meerstern/Nano_USB_Scroller/firm/mouse.c

#include <stdint.h>
#include <string.h>
#include "ch554.h"
#include "ch554_usb.h"
#include "mouse.h"

#define UsbSetupBuf ((USB_SETUP_REQ *)Ep0Buffer)
#define FIXED_ADDRESS_EP0_BUFFER    0x0000  
#define FIXED_ADDRESS_EP1_BUFFER    0x0010 

// Device Descriptor
__code uint8_t DevDesc[18] = 
{
	0x12, 0x01, 0x10, 0x01, 0x00, 0x00,	0x00, 0x08,
	VENDOR_ID, PRODUCT_ID, 0x00, 0x01, 0x01, 0x02,		
	0x00, 0x01
};

// Configuration Descriptor
__code uint8_t CfgDesc[59] =
{
	0x09, 0x02,	0x22, 0x00,	0x01, 0x01,	0x00, 0x80,		
	0x32, 0x09,	0x04, 0x00, 0x00, 0x01,	0x03, 0x01,		
	0x02, 0x00,	0x09, 0x21,	0x11, 0x01,	0x00, 0x01,		
	0x22, 0x34, 0x00, 0x07,	0x05, 0x81,	0x03, 0x04, 
	0x00, 0x0a
};

// HID Report Descriptor
__code uint8_t MouseRepDesc[52] =
{
	0x05, 0x01,	0x09, 0x02, 0xa1, 0x01,	0x09, 0x01,
	0xa1, 0x00,	0x05, 0x09,	0x19, 0x01,	0x29, 0x03,	
	0x15, 0x00,	0x25, 0x01,	0x95, 0x03,	0x75, 0x01,	
	0x81, 0x02,	0x95, 0x01,	0x75, 0x05,	0x81, 0x03,	
	0x05, 0x01,	0x09, 0x30,	0x09, 0x31,	0x09, 0x38,	
	0x15, 0x81,	0x25, 0x7f,	0x75, 0x08,	0x95, 0x03,	
	0x81, 0x06,	0xc0, 0xc0
};

// String Descriptor (Language)
__code unsigned char LangDesc[] = {0x04, 0x03, 0x09, 0x04};

// String Descriptor (Manufacturer)
__code unsigned char ManufDesc[] =
{
	sizeof(ManufDesc), 0x03, MANUFACTURER_DESCRIPTION
};

// String Descritor (Product)
__code unsigned char ProdDesc[] =
{
	sizeof(ProdDesc), 0x03, PRODUCT_DESCRIPTION
};

__xdata __at (FIXED_ADDRESS_EP0_BUFFER) uint8_t Ep0Buffer[DEFAULT_ENDP0_SIZE];	//Endpoint0 OUT&IN
__xdata __at (FIXED_ADDRESS_EP1_BUFFER) uint8_t Ep1Buffer[MAX_PACKET_SIZE];		//Endpoint1 IN

uint8_t SetupReq, SetupLen, UsbConfig;
USB_SETUP_REQ SetupReqBuf;
__code uint8_t *pDescr;

volatile __idata uint8_t RepDescSent;
volatile __idata uint8_t HIDDataSent;

uint8_t buttonsState = 0;

int8_t hidMouse[4] = 
{
	0x0,	// Buttons
	0x0,	// X
	0x0,	// Y
	0x0		// Wheel
};

void USBInterruptHandler( void ) __interrupt (INT_NO_USB)
{
	uint8_t len;

	if(UIF_TRANSFER)
	{
		switch (USB_INT_ST & (MASK_UIS_TOKEN | MASK_UIS_ENDP))
		{
			case UIS_TOKEN_IN | 1:
				UEP1_T_LEN = 0;
				UEP1_CTRL = UEP1_CTRL & ~MASK_UEP_T_RES | UEP_T_RES_NAK;
				HIDDataSent = 1;
				break;
			case UIS_TOKEN_SETUP | 0:
				len = USB_RX_LEN;
				if(len == (sizeof(USB_SETUP_REQ)))
				{
					SetupLen = UsbSetupBuf->wLengthL;
					if(UsbSetupBuf->wLengthH || SetupLen > 0x7f )
					{
						SetupLen = 0x7f;
					}
					len = 0;
					SetupReq = UsbSetupBuf->bRequest;								
					if ( ( UsbSetupBuf->bRequestType & USB_REQ_TYP_MASK ) != USB_REQ_TYP_STANDARD )
					{
						switch( SetupReq ) 
						{
							case 0x01: //GetReport
								 break;
							case 0x02: //GetIdle
								 break;	
							case 0x03: //GetProtocol
								 break;				
							case 0x09: //SetReport										
								 break;
							case 0x0a: //SetIdle
								 break;	
							case 0x0b: //SetProtocol
								 break;
							default:
								 len = 0xff;
								 break;
						  }	
					}
					else
					{
						switch(SetupReq)
						{
							case USB_GET_DESCRIPTOR:
								switch(UsbSetupBuf->wValueH)
								{
								case 1:
									pDescr = DevDesc;
									len = sizeof(DevDesc);
									break;
								case 2:
									pDescr = CfgDesc;
									len = sizeof(CfgDesc);
									break;
								case 3:
									if(UsbSetupBuf->wValueL == 0)
									{
										pDescr = LangDesc;
										len = sizeof(LangDesc);
									}
									else if(UsbSetupBuf->wValueL == 1)
									{
										pDescr = ManufDesc;
										len = sizeof(ManufDesc);
									}
									else if(UsbSetupBuf->wValueL == 2)
									{
										pDescr = ProdDesc;
										len = sizeof(ProdDesc);
									}
									else
									{
										len = 0xff;
									}
									break;

								case 0x22:
									if(UsbSetupBuf->wIndexL == 0)
									{
										pDescr = MouseRepDesc;
										len = sizeof(MouseRepDesc);
										RepDescSent = 1;
									}
									else
									{
										len = 0xff;
									}
									break;
								default:
									len = 0xff;
									break;
								}
								if ( SetupLen > len )
								{
									SetupLen = len;
								}
								len = SetupLen >= 8 ? 8 : SetupLen;
								memcpy(Ep0Buffer, pDescr, len);
								SetupLen -= len;
								pDescr += len;
								break;
							case USB_SET_ADDRESS:
								SetupLen = UsbSetupBuf->wValueL;
								break;
							case USB_GET_CONFIGURATION:
								Ep0Buffer[0] = UsbConfig;
								if ( SetupLen >= 1 )
								{
									len = 1;
								}
								break;
							case USB_SET_CONFIGURATION:
								UsbConfig = UsbSetupBuf->wValueL;
								break;
							case 0x0a:
								break;
							case USB_CLEAR_FEATURE:
								if ( ( UsbSetupBuf->bRequestType & USB_REQ_RECIP_MASK ) == USB_REQ_RECIP_ENDP )
								{
									switch( UsbSetupBuf->wIndexL )
									{
									case 0x81:
										UEP1_CTRL = UEP1_CTRL & ~( bUEP_T_TOG | MASK_UEP_T_RES ) | UEP_T_RES_NAK;
										break;
									case 0x01:
										UEP1_CTRL = UEP1_CTRL & ~( bUEP_R_TOG | MASK_UEP_R_RES ) | UEP_R_RES_ACK;
										break;
									default:
										len = 0xff;
										break;
									}
								}
								else
								{
									len = 0xff;
								}
								break;
							case USB_SET_FEATURE:
								if( ( UsbSetupBuf->bRequestType & 0x1f ) == 0x00 )
								{
									if( ( ( ( uint16_t )UsbSetupBuf->wValueH << 8 ) | UsbSetupBuf->wValueL ) == 0x01 )
									{
										if( CfgDesc[ 7 ] & 0x20 )
										{
										}
										else
										{
											len = 0xff;
										}
									}
									else
									{
										len = 0xff;
									}
								}
								else if( ( UsbSetupBuf->bRequestType & 0x1f ) == 0x02 )
								{
									if( ( ( ( uint16_t )UsbSetupBuf->wValueH << 8 ) | UsbSetupBuf->wValueL ) == 0x00 )
									{
										switch( ( ( uint16_t )UsbSetupBuf->wIndexH << 8 ) | UsbSetupBuf->wIndexL )
										{
										case 0x81:
											UEP1_CTRL = UEP1_CTRL & (~bUEP_T_TOG) | UEP_T_RES_STALL;
											break;
										default:
											len = 0xff;
											break;
										}
									}
									else
									{
										len = 0xff;
									}
								}
								else
								{
									len = 0xff;
								}
								break;
							case USB_GET_STATUS:
								Ep0Buffer[0] = 0x00;
								Ep0Buffer[1] = 0x00;
								if ( SetupLen >= 2 )
								{
									len = 2;
								}
								else
								{
									len = SetupLen;
								}
								break;
							default:
								len = 0xff;
								break;
						}
					}
				}
				else
				{
					len = 0xff;
				}
				if(len == 0xff)
				{
					SetupReq = 0xff;
					UEP0_CTRL = bUEP_R_TOG | bUEP_T_TOG | UEP_R_RES_STALL | UEP_T_RES_STALL;
				}
				else if(len <= 8)
				{
					UEP0_T_LEN = len;
					UEP0_CTRL = bUEP_R_TOG | bUEP_T_TOG | UEP_R_RES_ACK | UEP_T_RES_ACK;
				}
				else
				{
					UEP0_T_LEN = 0;
					UEP0_CTRL = bUEP_R_TOG | bUEP_T_TOG | UEP_R_RES_ACK | UEP_T_RES_ACK;
				}
				break;
			case UIS_TOKEN_IN | 0:
				switch(SetupReq)
				{
					case USB_GET_DESCRIPTOR:
						len = SetupLen >= 8 ? 8 : SetupLen;
						memcpy( Ep0Buffer, pDescr, len );
						SetupLen -= len;
						pDescr += len;
						UEP0_T_LEN = len;
						UEP0_CTRL ^= bUEP_T_TOG;
						break;
					case USB_SET_ADDRESS:
						USB_DEV_AD = USB_DEV_AD & bUDA_GP_BIT | SetupLen;
						UEP0_CTRL = UEP_R_RES_ACK | UEP_T_RES_NAK;
						break;
					default:
						UEP0_T_LEN = 0;
						UEP0_CTRL = UEP_R_RES_ACK | UEP_T_RES_NAK;
						break;
				}
				break;
			case UIS_TOKEN_OUT | 0:
				UEP0_T_LEN = 0;
				UEP0_CTRL = UEP_R_RES_ACK | UEP_T_RES_ACK;
				break;
			default:
				break;
			}
			UIF_TRANSFER = 0;
	}
	if(UIF_BUS_RST)
	{
		UEP0_CTRL = UEP_R_RES_ACK | UEP_T_RES_NAK;
		UEP1_CTRL = bUEP_AUTO_TOG | UEP_R_RES_ACK;
		UEP2_CTRL = bUEP_AUTO_TOG | UEP_R_RES_ACK | UEP_T_RES_NAK;
		USB_DEV_AD = 0x00;
		UIF_SUSPEND = 0;
		UIF_TRANSFER = 0;
		UIF_BUS_RST = 0;
	}
	if (UIF_SUSPEND)
	{
		UIF_SUSPEND = 0;
	}
	else {
		USB_INT_FG = 0xff;
	}
}

void hidValueHandle(uint8_t button, int8_t x, int8_t y, int8_t wheel)
{
	HIDDataSent = 0;		
	hidMouse[0] = button&MOUSE_BUTTONS_MASK;
	hidMouse[1] = x;
	hidMouse[2] = y;
	hidMouse[3] = wheel;
	memcpy(Ep1Buffer, hidMouse, sizeof(hidMouse));
	UEP1_T_LEN = sizeof(hidMouse);
	UEP1_CTRL = UEP1_CTRL & ~MASK_UEP_T_RES | UEP_T_RES_ACK;
	while(HIDDataSent == 0) {}
}

void mouse_init()
{
	IE_USB = 0;
	USB_CTRL = 0x00;
	UEP0_DMA = (uint16_t)Ep0Buffer;
	UEP1_DMA = (uint16_t)Ep1Buffer;
	UEP4_1_MOD = ~(bUEP4_RX_EN | bUEP4_TX_EN | bUEP1_RX_EN | bUEP1_BUF_MOD) | bUEP4_TX_EN;
	UEP0_CTRL = UEP_R_RES_ACK | UEP_T_RES_NAK;
	UEP1_CTRL = bUEP_T_TOG | UEP_T_RES_NAK;
	UEP1_T_LEN = 0;

	USB_DEV_AD = 0x00;
	UDEV_CTRL = bUD_PD_DIS;
	USB_CTRL = bUC_DEV_PU_EN | bUC_INT_BUSY | bUC_DMA_EN;

	UDEV_CTRL |= bUD_PORT_EN;
	USB_INT_FG = 0xff;
	USB_INT_EN = bUIE_SUSPEND | bUIE_TRANSFER | bUIE_BUS_RST;
	IE_USB = 1;

	RepDescSent = 0;
	EA = 1;
	while(RepDescSent == 0) {};
}
